Hakand6/Arduino-Nano-Wireless-NRF-RC-Car/rc kumanda/rc kumada kapak.stl

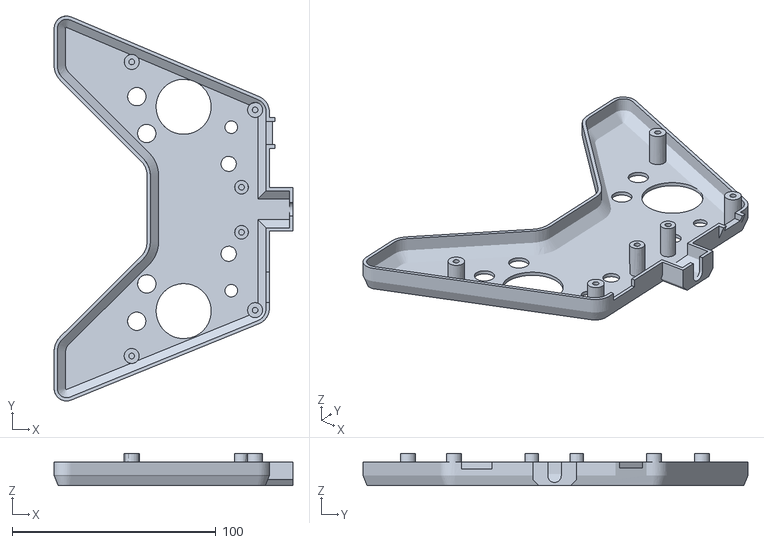
[picture p15: CAD file, 2026-09-17]
rc kumanda/rc kumada kapak.stl
117.1 x 188.8 x 15.9
