Hakand6/Arduino-Nano-Wireless-NRF-RC-Car/amortısor/obj_1_实体1.stl

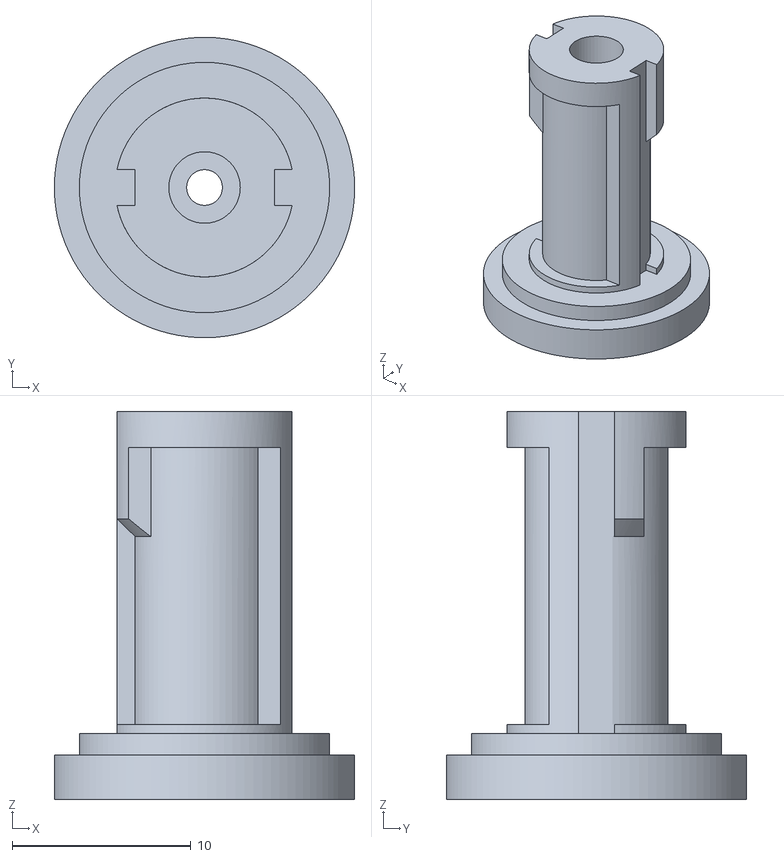
[picture p17: CAD file, 2026-09-17]
amortısor/obj_1_实体1.stl
16.8 x 16.8 x 21.7
