Hakand6/Arduino-Nano-Wireless-NRF-RC-Car/rc kumanda/rc kumada kasa.stl

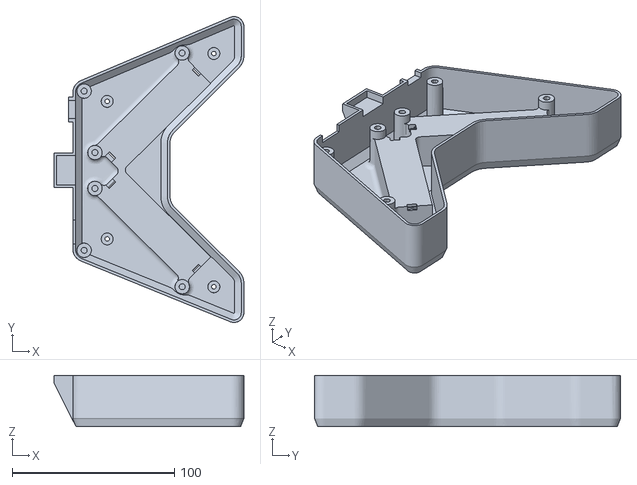
[picture p18: CAD file, 2026-09-17]
rc kumanda/rc kumada kasa.stl
117.1 x 188.8 x 31.7
