Hakand6/Arduino-Nano-Wireless-NRF-RC-Car/3d Printed Files/ServoMount.STL

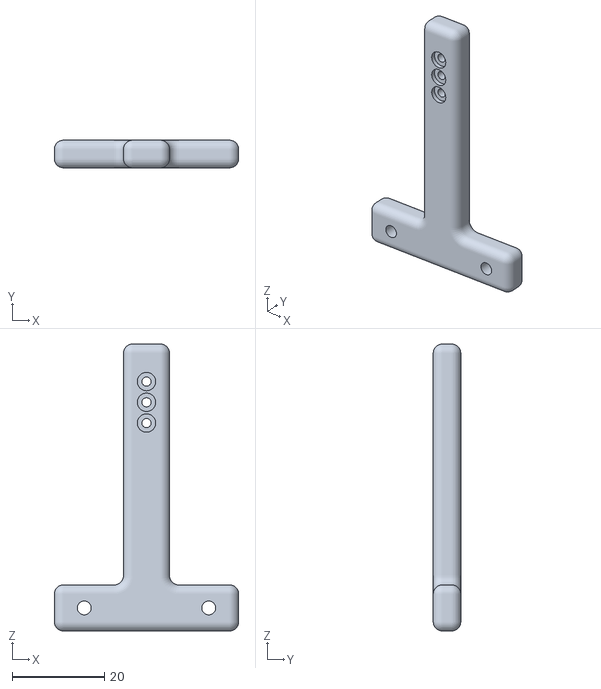
[picture p20: CAD file, 2026-09-17]
3d Printed Files/ServoMount.STL
40.0 x 6.00 x 62.2
