Hakand6/Arduino-Nano-Wireless-NRF-RC-Car/3d Printed Files/Suspension Arm DRIVING WHEEL.STL

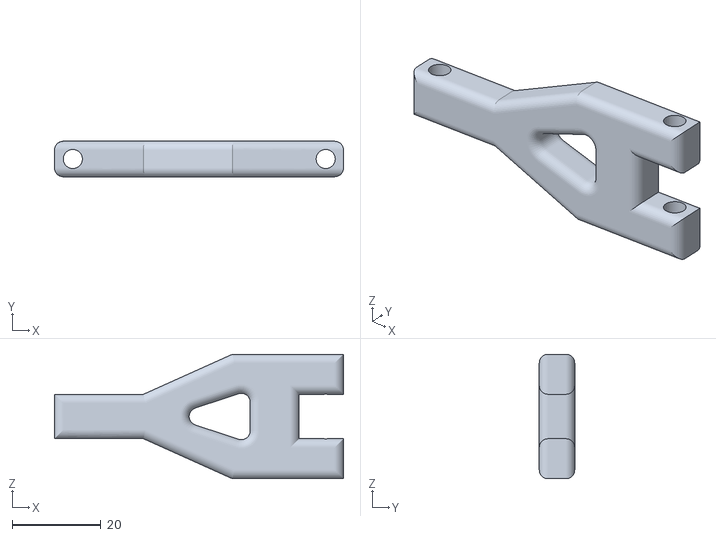
[picture p21: CAD file, 2026-09-17]
3d Printed Files/Suspension Arm DRIVING WHEEL.STL
65.0 x 8.00 x 28.0
