Hakand6/Arduino-Nano-Wireless-NRF-RC-Car/3d Printed Files/Wheel Spacer.STL

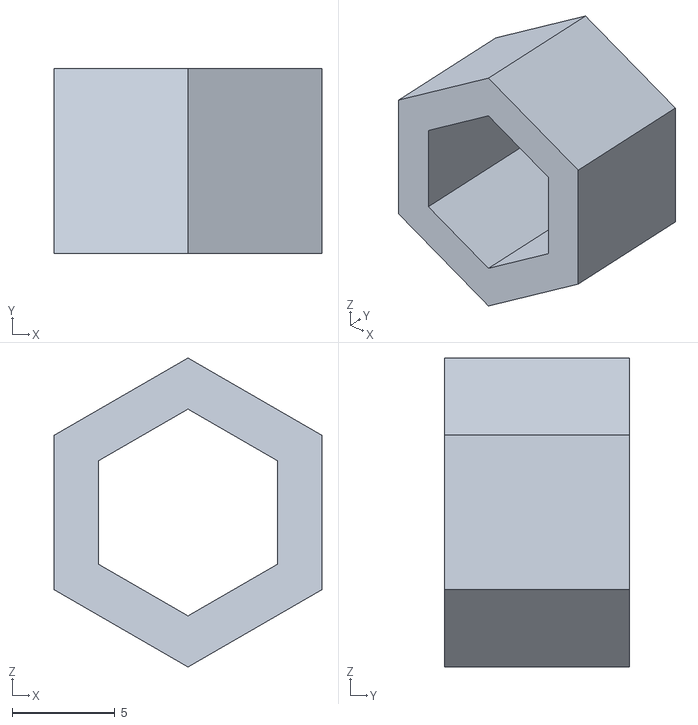
[picture p22: CAD file, 2026-09-17]
3d Printed Files/Wheel Spacer.STL
13.0 x 9.00 x 15.0
