Hakand6/Arduino-Nano-Wireless-NRF-RC-Car/3d Printed Files/Steering Connector.STL

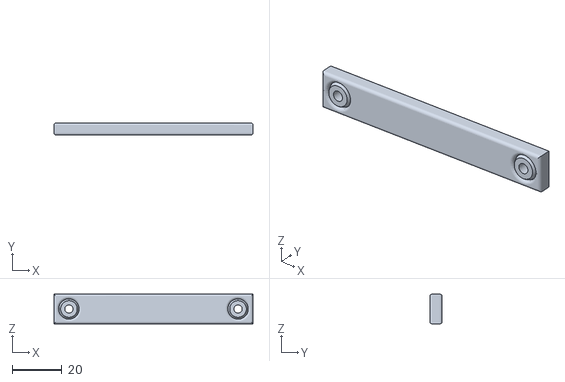
[picture p23: CAD file, 2026-09-17]
3d Printed Files/Steering Connector.STL
80.0 x 5.00 x 12.0
