Hakand6/Arduino-Nano-Wireless-NRF-RC-Car/3d Printed Files/Frame.STL

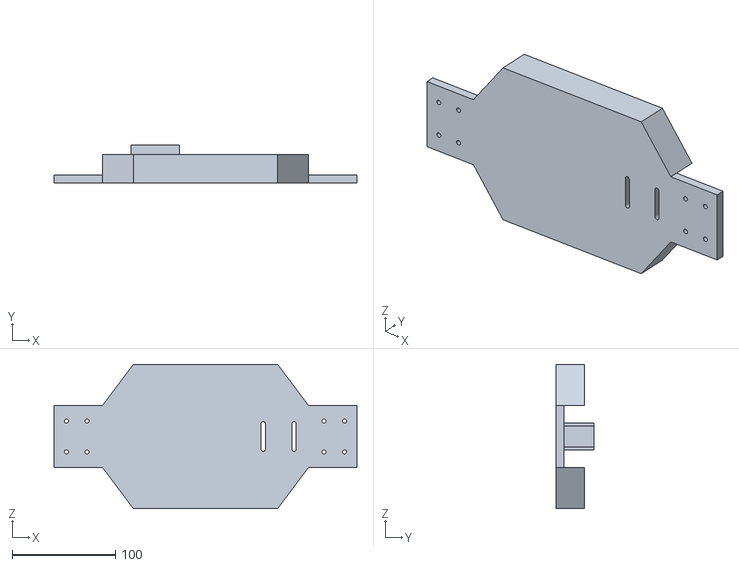
[picture p24: CAD file, 2026-09-17]
3d Printed Files/Frame.STL
294.0 x 36.5 x 140.0
