Hakand6/Arduino-Nano-Wireless-NRF-RC-Car/3d Printed Files/Rear Wheel Connector.STL

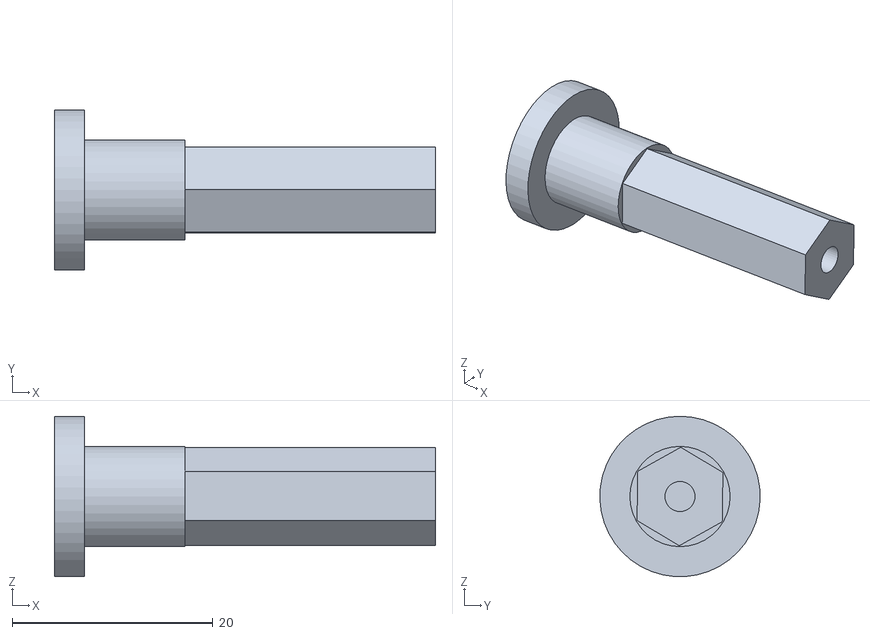
[picture p25: CAD file, 2026-09-17]
3d Printed Files/Rear Wheel Connector.STL
38.0 x 16.0 x 16.0
