Hakand6/Arduino-Nano-Wireless-NRF-RC-Car/3d Printed Files/Steering Arm Top.STL

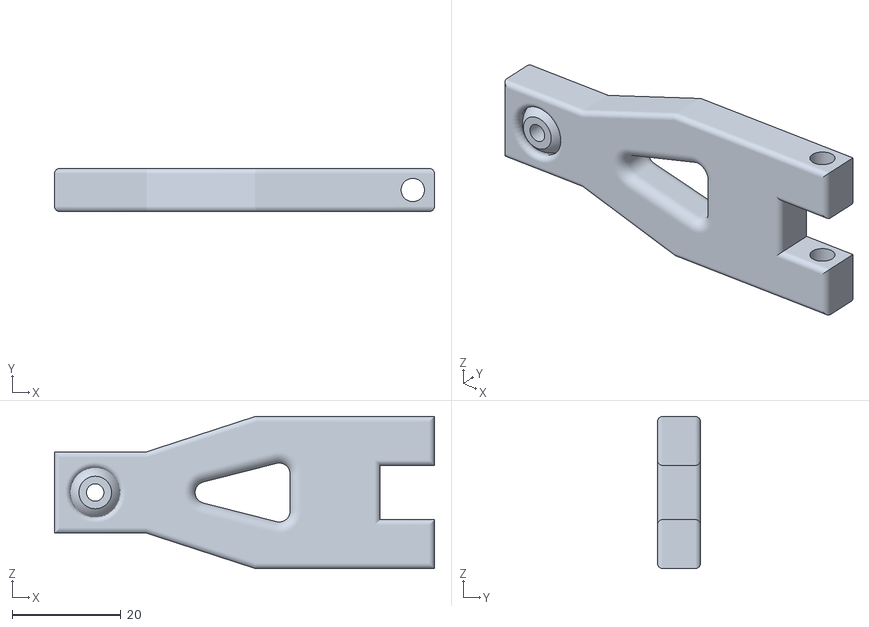
[picture p26: CAD file, 2026-09-17]
3d Printed Files/Steering Arm Top.STL
70.0 x 8.00 x 28.0
