Hakand6/Arduino-Nano-Wireless-NRF-RC-Car/3d Printed Files/Spacer.STL

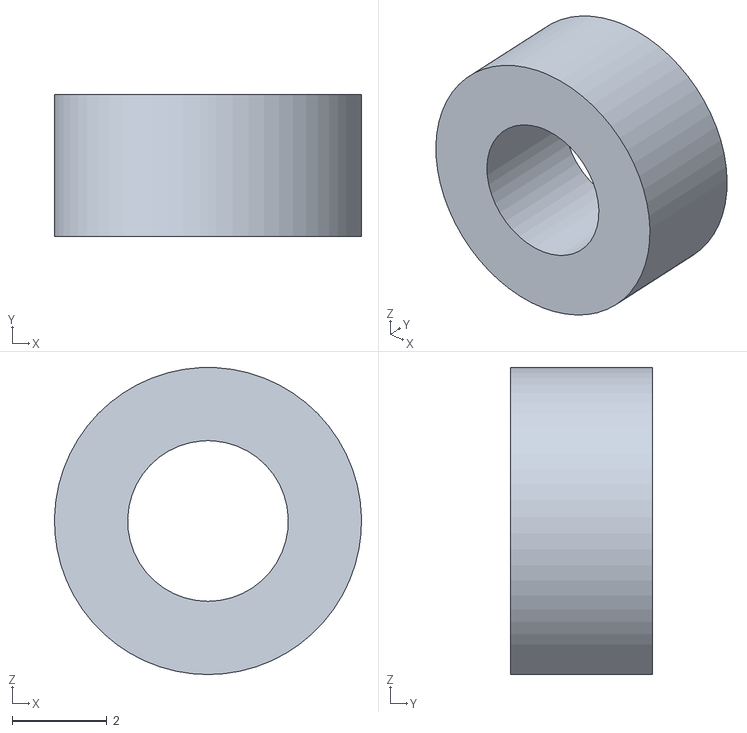
[picture p27: CAD file, 2026-09-17]
3d Printed Files/Spacer.STL
6.50 x 3.00 x 6.50
