Hakand6/Arduino-Nano-Wireless-NRF-RC-Car/3d Printed Files/Large Bevel Gear.STL

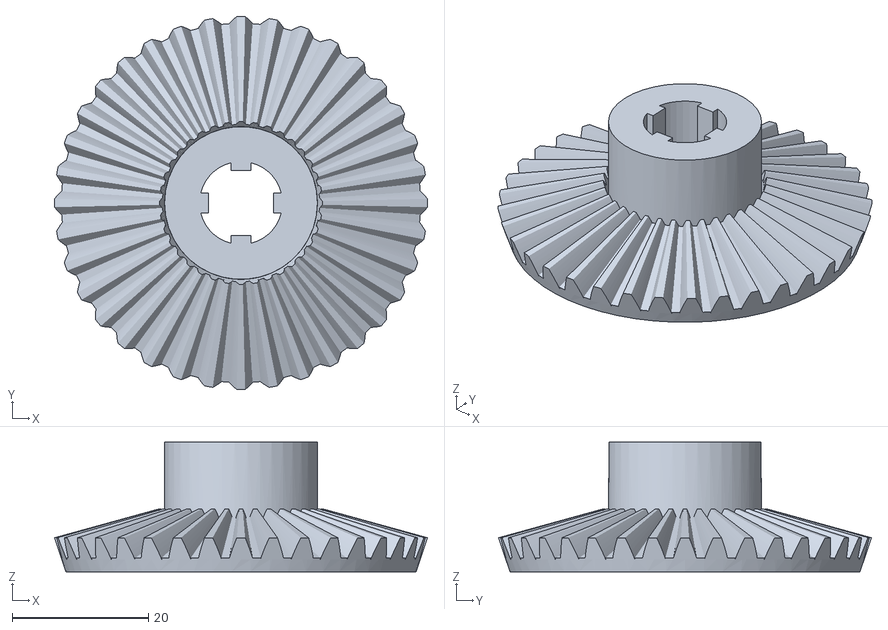
[picture p28: CAD file, 2026-09-17]
3d Printed Files/Large Bevel Gear.STL
54.8 x 54.8 x 19.1
