Hakand6/Arduino-Nano-Wireless-NRF-RC-Car/3d Printed Files/Front Wheel Hub.STL

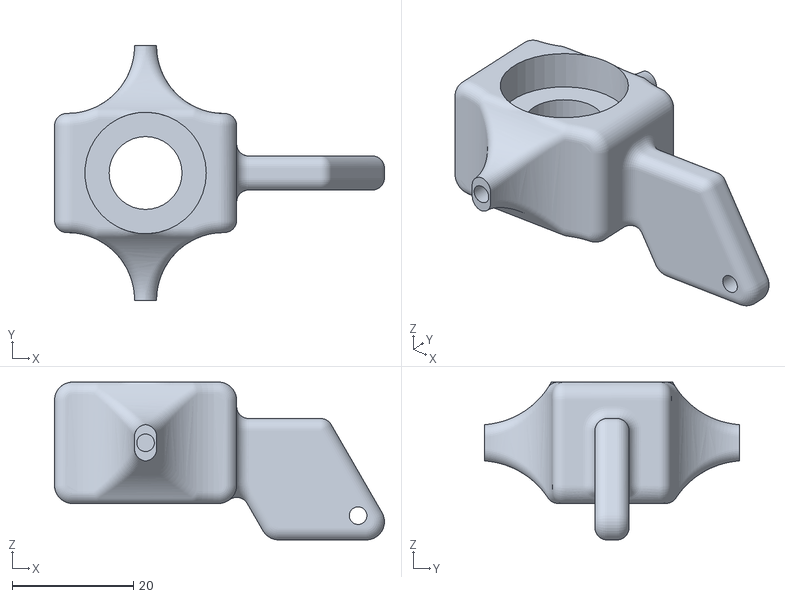
[picture p29: CAD file, 2026-09-17]
3d Printed Files/Front Wheel Hub.STL
54.4 x 42.0 x 26.0
