Hakand6/Arduino-Nano-Wireless-NRF-RC-Car/3d Printed Files/Bumper.STL

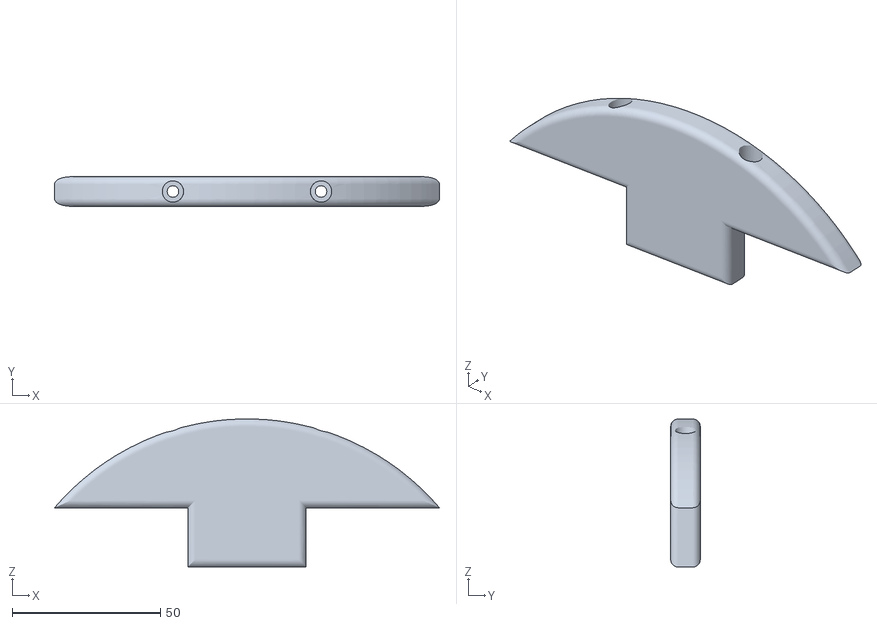
[picture p30: CAD file, 2026-09-17]
3d Printed Files/Bumper.STL
130.0 x 10.0 x 50.0
