Hakand6/Arduino-Nano-Wireless-NRF-RC-Car/3d Printed Files/Rear Wheel Hub Left.STL

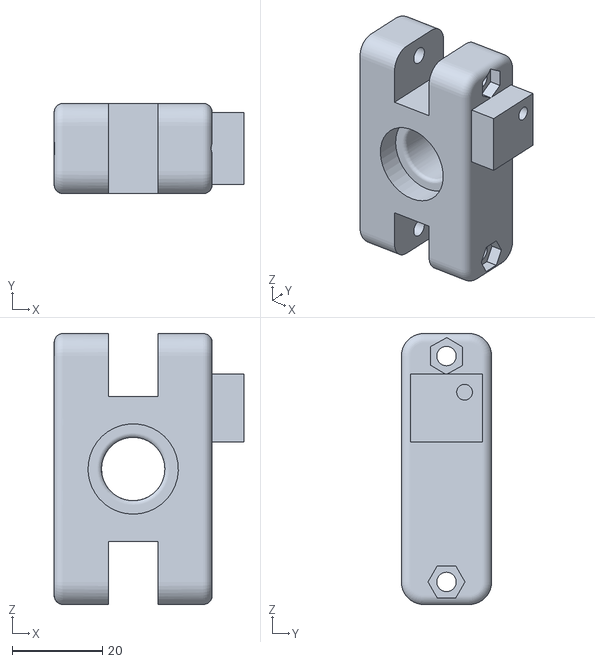
[picture p31: CAD file, 2026-09-17]
3d Printed Files/Rear Wheel Hub Left.STL
42.0 x 20.0 x 60.0
