Hakand6/Arduino-Nano-Wireless-NRF-RC-Car/3d Printed Files/Shock Absorber Extension - Rear Suspension Hub.STL

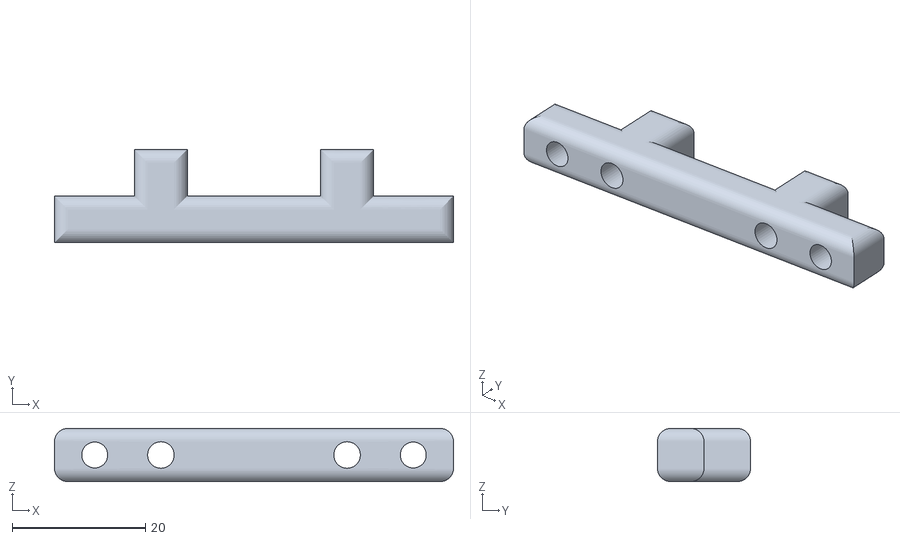
[picture p32: CAD file, 2026-09-17]
3d Printed Files/Shock Absorber Extension - Rear Suspension Hub.STL
60.0 x 14.0 x 8.00
